frostbyte-ninja/PirBOX-LITE/Code/PirBox-Lite/test/main_test.cpp

#include <cstdlib>

#include <gmock/gmock.h>

int
main(int argc, char** argv)
{
  ::testing::InitGoogleMock(&argc, argv);

  if (RUN_ALL_TESTS()) {
  }

  // Always return zero-code and allow PlatformIO to parse results
  return EXIT_SUCCESS;
}
